dumpmemory/PH60/Case/PH60Rev2/inner_mid.3mf

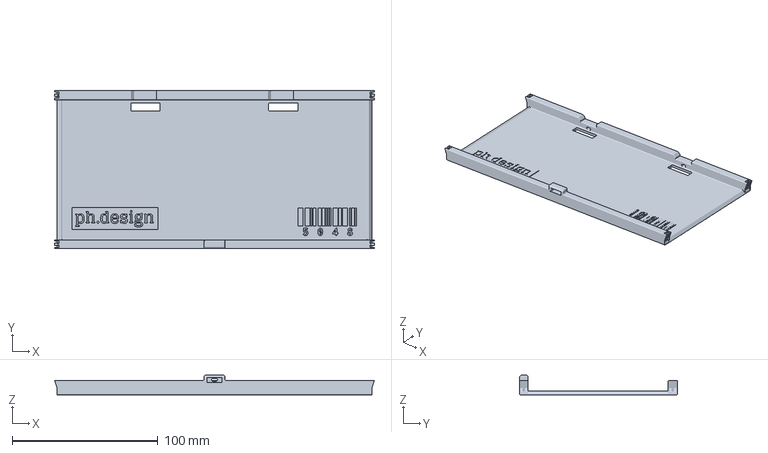
[picture p14: CAD file, 2025-04-19]
Case/PH60Rev2/inner_mid.3mf
219.3 x 108.5 x 13.4 mm
