dumpmemory/PH60/Case/PH60i/inner.3mf

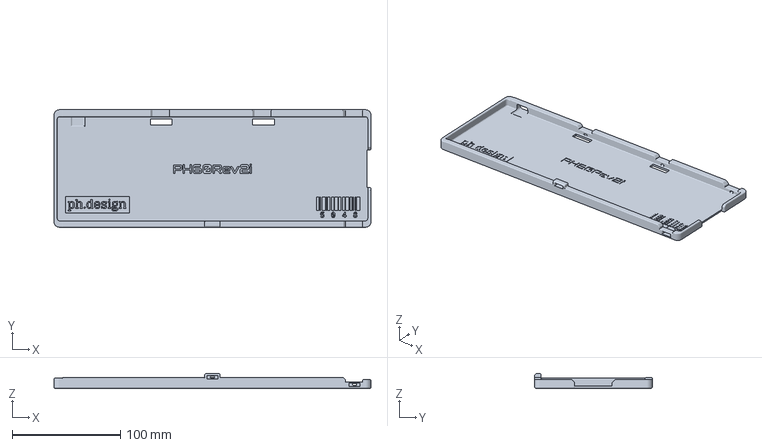
[picture p15: CAD file, 2025-04-19]
Case/PH60i/inner.3mf
292.6 x 108.5 x 13.4 mm
