dumpmemory/PH60/Case/PH60Rev2/For Bambu Studio.3mf

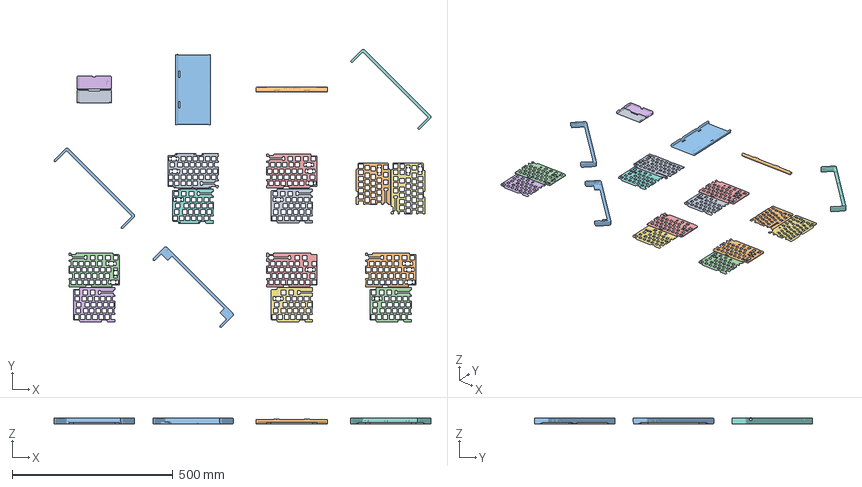
[picture p16: CAD file, 2025-04-19]
Case/PH60Rev2/For Bambu Studio.3mf
1171.8 x 864.8 x 19.7 mm
thick_plate_r_(1) x 2
ansir x 2
hhkb_outer_case_b
ansil x 2
hhkbl
inner_case_left
hhkbr
outer_case_2
inner_case_right
pillow
inner_case_mid
thick_plate_l_(1) x 2
63r
63l
outer_case_1
