dumpmemory/PH60/Plates_Rev2/3D Model/CAD/LS64_SSPACE_SB.step

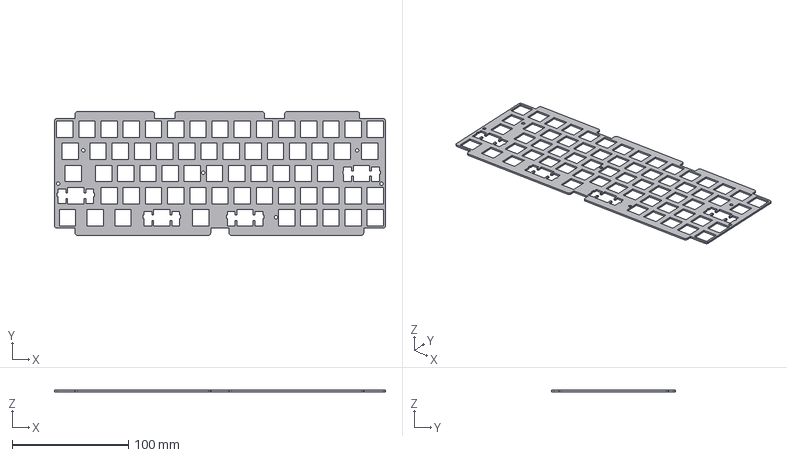
[picture p17: CAD file, 2025-06-04]
Plates_Rev2/3D Model/CAD/LS64_SSPACE_SB.step
284.2 x 106.2 x 1.50 mm
