dumpmemory/PH60/Plates_Rev2/3D Model/CAD/WKL_PCBS.step

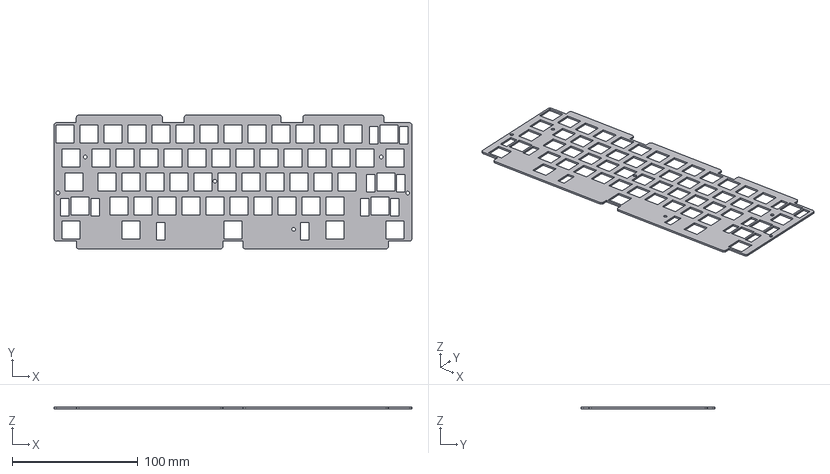
[picture p18: CAD file, 2025-05-10]
Plates_Rev2/3D Model/CAD/WKL_PCBS.step
284.2 x 106.2 x 1.50 mm
