dumpmemory/PH60/Plates_Rev2/3D Model/CAD/HHKB_thick.step

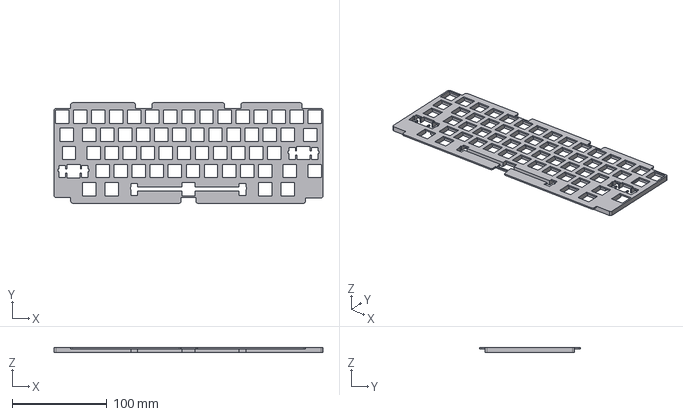
[picture p19: CAD file, 2025-04-19]
Plates_Rev2/3D Model/CAD/HHKB_thick.step
284.2 x 106.2 x 5.00 mm
